MelvinQM/IOT-Personal/docs/assets/images/dc-dc-holder1.png

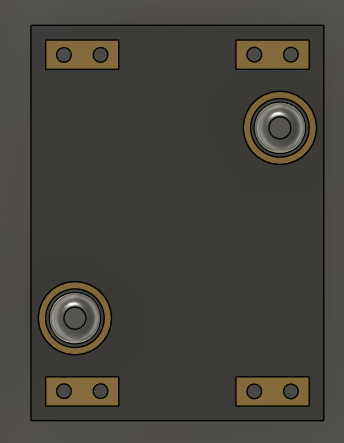
docs/assets/images/dc-dc-holder1.png
