MelvinQM/IOT-Personal/docs/assets/images/MPU6050-diagram.png

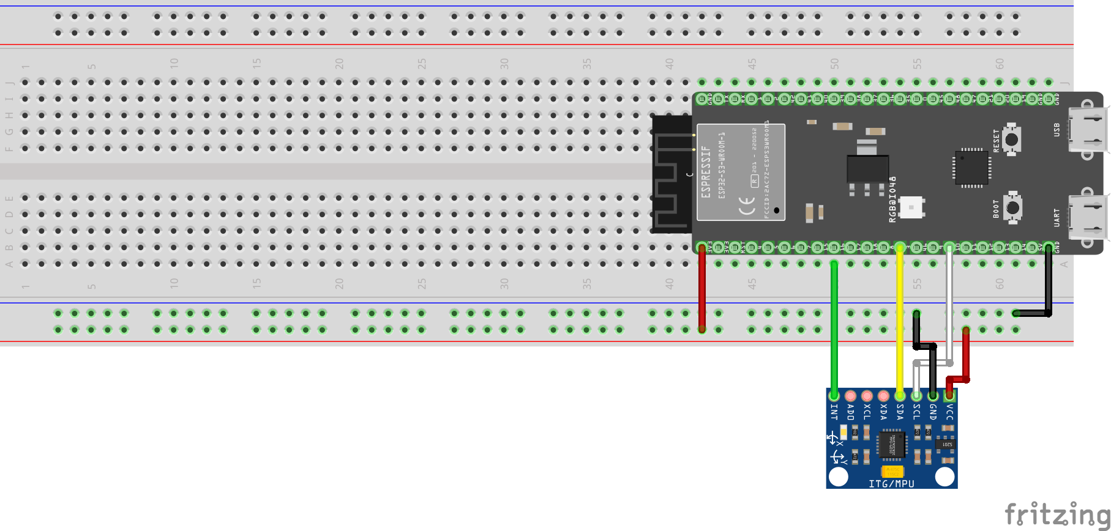
docs/assets/images/MPU6050-diagram.png
