MelvinQM/IOT-Personal/docs/assets/images/mpuholder-1.png

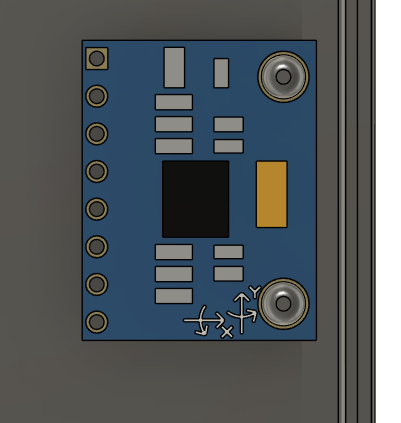
docs/assets/images/mpuholder-1.png
