MelvinQM/IOT-Personal/docs/assets/images/rawmpudata.png

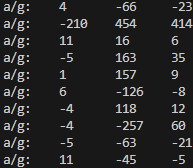
docs/assets/images/rawmpudata.png
