MelvinQM/IOT-Personal/docs/assets/sprites/background-2.png

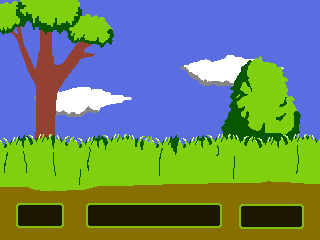
docs/assets/sprites/background-2.png
