MelvinQM/IOT-Personal/docs/assets/sprites/background.png

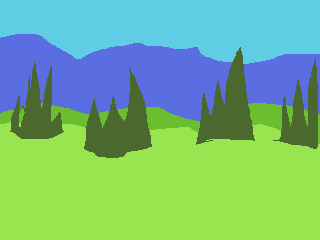
docs/assets/sprites/background.png
