MelvinQM/IOT-Personal/docs/assets/images/components/esp32-s3.png

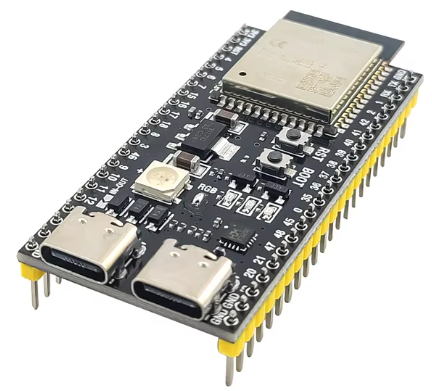
docs/assets/images/components/esp32-s3.png
