MelvinQM/IOT-Personal/embedded/ESP32-Controller/include/udp_connection.h

/*
 * Author: Melvin Moes
 * Date: October 14, 2024
 * Description: This header defines the UdpConnection class, which manages UDP communication for sending data 
 * from the gyroscope and joystick. It provides methods to initialize the connection, An option is also present to construct 
 * JSON documents containing relevant data and send them over the UDP connection. 
 * License: This project is licensed under the MIT License.
 */

#ifndef UDP_CONNECTION_H
#define UDP_CONNECTION_H

#include "utilities.h"
#include "Wifi.h"
#include "WiFiUdp.h"

class UdpConnection
{
    public:
        void init();
        void sendJsonData(JsonDocument &doc, bool response = false, bool retry = false);
    private:
        const char *kUDPAddress = "192.168.1.1";
        const int kUDPPort = 44444;
        const char *kSSID = "HootPursuitConsoleAP";
        const char *kPassword = "hootpursuitaccess";
        WiFiUDP udp;

};

#endif
