MelvinQM/IOT-Personal/embedded/ESP32-Controller/src/Joystick.cpp

/*
 * Author: Melvin Moes
 * Date: October 18, 2024
 * Description: An implementation of the Joystick class, which handles the initialization and 
 * reading of joystick input. It includes methods for initializing joystick pins, reading the joystick 
 * button state, and normalizing joystick axis values to a specific range.
 * License: This project is licensed under the MIT License.
 */

#include "joystick.h"

void Joystick::init()
{
    pinMode(JOYSTICK_VRX_PIN, INPUT);
    pinMode(JOYSTICK_VRY_PIN, INPUT);
    pinMode(JOYSTICK_SW_PIN, INPUT_PULLUP);
}

bool Joystick::readJoystickClick()
{
    return !digitalRead(JOYSTICK_SW_PIN);
}

void Joystick::readJoystickAxis()
{
    // Serial.println("X: " + String(analogRead(JOYSTICK_VRX_PIN)) + " Y: " + String(analogRead(JOYSTICK_VRY_PIN)));
    normalizeAxis(analogRead(JOYSTICK_VRX_PIN), analogRead(JOYSTICK_VRY_PIN));
    // Serial.println("X: " + String(data.x) + " Y: " + String(data.y));
}

void Joystick::normalizeAxis(int x, int y)
{
    float nX = (x - RANGE_IN_MIN) * (RANGE_OUT_MAX - RANGE_OUT_MIN) / (RANGE_IN_MAX - RANGE_IN_MIN) + (RANGE_OUT_MIN);
    float nY = (y - RANGE_IN_MIN) * (RANGE_OUT_MAX - RANGE_OUT_MIN) / (RANGE_IN_MAX - RANGE_IN_MIN) + (RANGE_OUT_MIN);
    
    // Cut off the decimals
    nX = round(nX * NORMALIZE_FACTOR_JOYSTICK) / NORMALIZE_FACTOR_JOYSTICK;
    nY = round(nY * NORMALIZE_FACTOR_JOYSTICK) / NORMALIZE_FACTOR_JOYSTICK;

    if (fabs(nX) < JOYSTICK_DEAD_ZONE) {
        nX = 0.0;
    }
    if (fabs(nY) < JOYSTICK_DEAD_ZONE) {
        nY = 0.0;
    }

    //"-" to prevent inverse vertical controls, storing x as y and y as x to have correct movement
    data = {nY, -nX};
}

JoystickData Joystick::getAxis()
{
    return data;
}
