MelvinQM/IOT-Personal/embedded/ESP32-Display-Board/include/utilities.h

/*
 * Author: Melvin Moes
 * Date: November 6, 2024
 * Description: This header defines various utility constants, pin assignments, and data structures used in the project. 
 * It also includes definitions for a button pin and data structures for joystick and gyro data.
 * License: This project is licensed under the MIT License.
 */

#ifndef UTILITIES_H
#define UTILITIES_H

#include <Arduino.h>
#include <ArduinoJson.h>

// General settings
#define BAUD_RATE           115200
#define TIMEOUT_DELAY       1000
#define BIG_TIMEOUT_DELAY   5000
#define HIGHSCORE_KEEPALIVE 10000


// Display settings and configurations
#define SCREEN_WIDTH    320
#define SCREEN_HEIGHT   240
#define SCREEN_ORIGIN_X 0
#define SCREEN_ORIGIN_Y 0
#define SCREEN_ROTATION 1   // Landscape

// Game settings
#define CURSOR_SPEED    10
#define USE_GYRO        false
#define EXTRA_SCORE_MAX 50
#define EXTRA_SCORE_DIVISION_FACTOR (SCREEN_WIDTH / EXTRA_SCORE_MAX)

// Pin definitions
#define BUTTON_PIN  22
#define LED_PIN_R       4
#define LED_PIN_G       16
#define LED_PIN_B       17
#define LED_R_CHANNEL 0
#define LED_G_CHANNEL 1
#define LED_B_CHANNEL 2
#define LED_DEFAULT_BRIGHTNESS 0.1

// Wifi settings
#define WIFI_TIMEOUT    10000
#define UDP_DELAY       10
#define HIGHSCORE_AMOUNT 10

// Defining the JSON method names
#define TRIGGER_METHOD              "trigger"
#define JOYSTICK_CLICK_METHOD       "joystickClick"
#define CONTROLLER_AXIS_DATA_METHOD "axisData"

/**
 * @enum {int} Difficulty - Enumeration for the game difficulty levels.
 * @property {int} EASY - Easy level difficulty.
 * @property {int} NORMAL - Normal level difficulty.
 * @property {int} HARD - Hard level difficulty.
 */
enum Difficulty {
    EASY = 1,
    NORMAL = 2,
    HARD = 3
};

/**
 * @struct GameSettings
 * @brief A structure that holds the current game settings, including session ID, player ID, difficulty, score, and gyro usage.
 * @property {unsigned int} sessionId - The unique session ID for the current game session.
 * @property {unsigned int} playerId - The unique player ID associated with the session.
 * @property {Difficulty} difficultyId - The difficulty level selected for the game.
 * @property {unsigned int} score - The current score of the player.
 * @property {boolean} useGyro - Whether the gyro is used for game control.
 */
struct GameSettings {
    unsigned int sessionId;
    unsigned int playerId;
    Difficulty difficultyId;
    unsigned int score;
    boolean useGyro;
};

#endif
